Arsenic-Tech/LAV1/IMGS/vsp5 cl graph.png

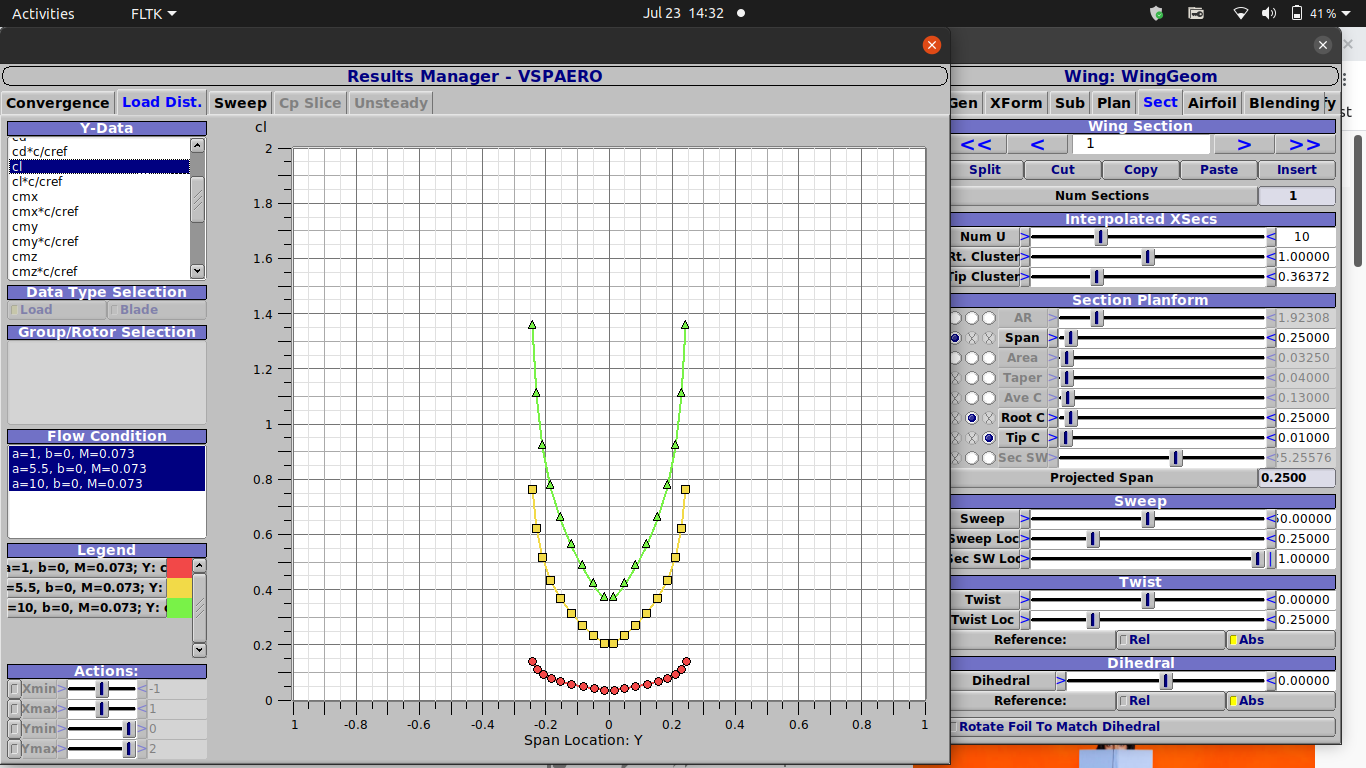
IMGS/vsp5 cl graph.png
