Arsenic-Tech/LAV1/IMGS/vsp7.1.convergence.CDtot.png

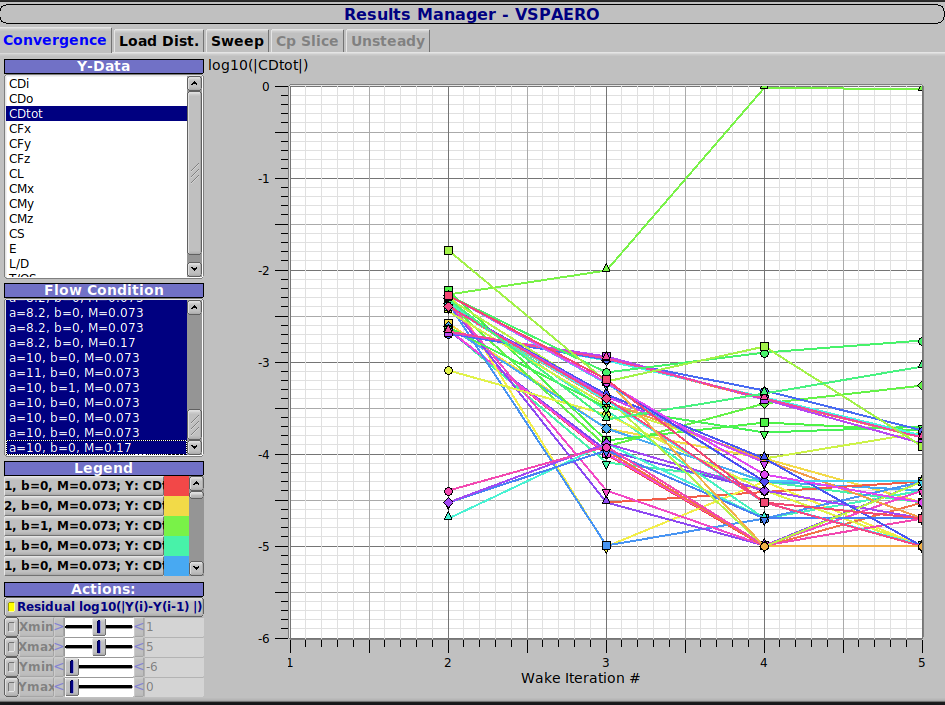
IMGS/vsp7.1.convergence.CDtot.png
