Arsenic-Tech/LAV1/IMGS/vsp7.1.convergence.L-D.png

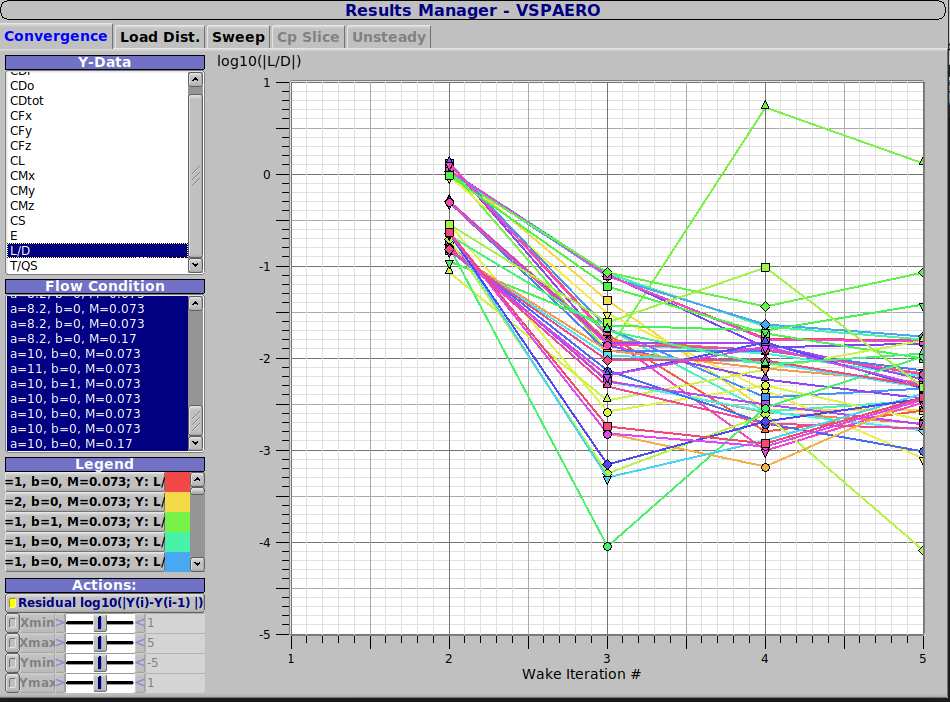
IMGS/vsp7.1.convergence.L-D.png
