Arsenic-Tech/LAV1/IMGS/vsp712.png

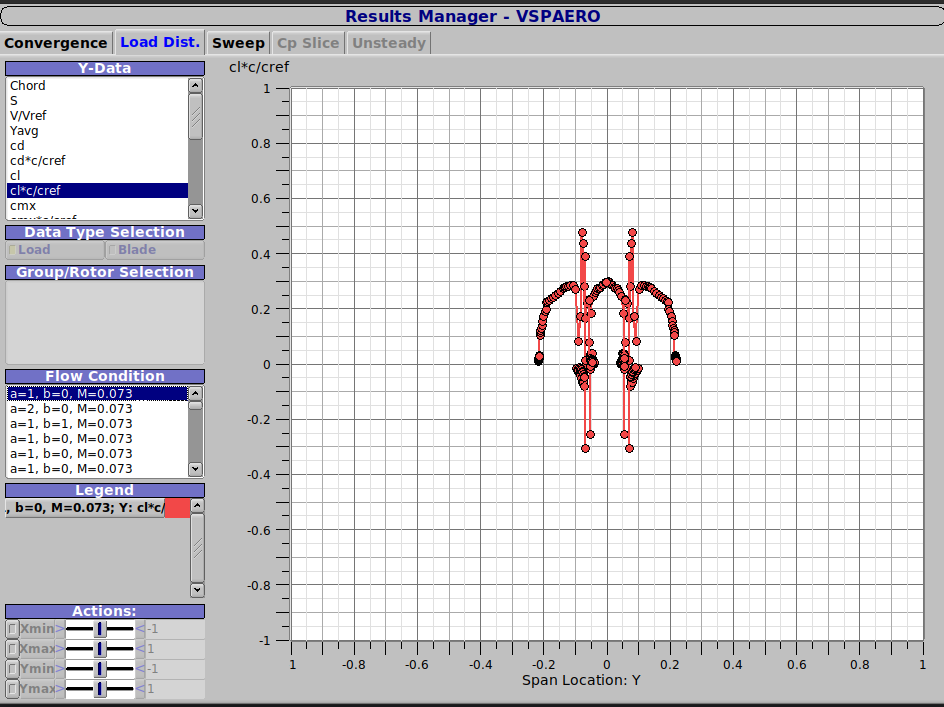
IMGS/vsp712.png
