Arsenic-Tech/LAV1/IMGS/vsp713.png

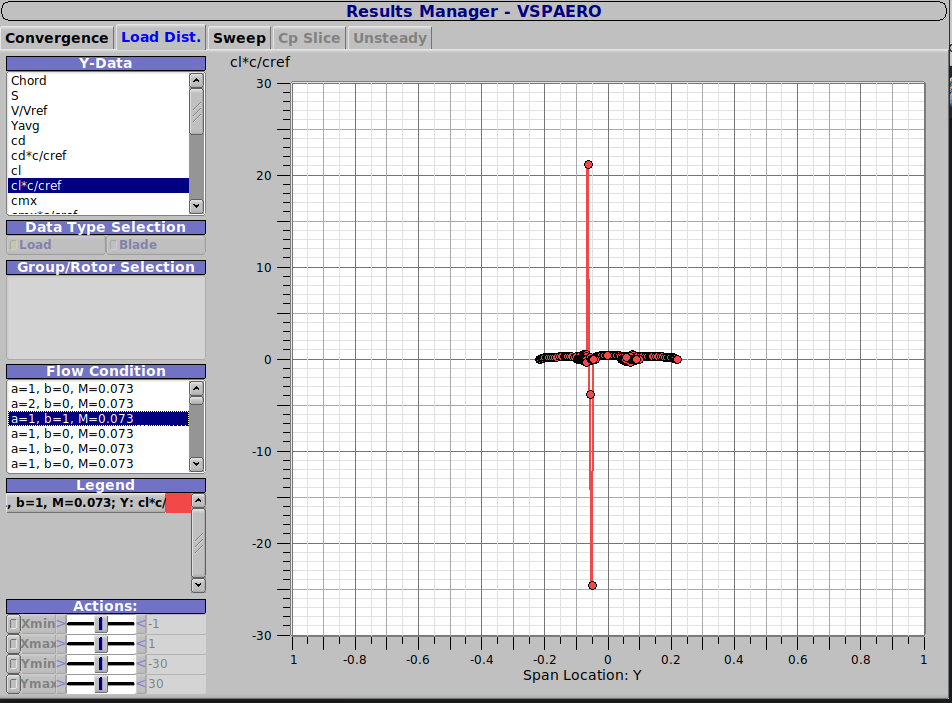
IMGS/vsp713.png
