Arsenic-Tech/LAV1/IMGS/vsp717.png

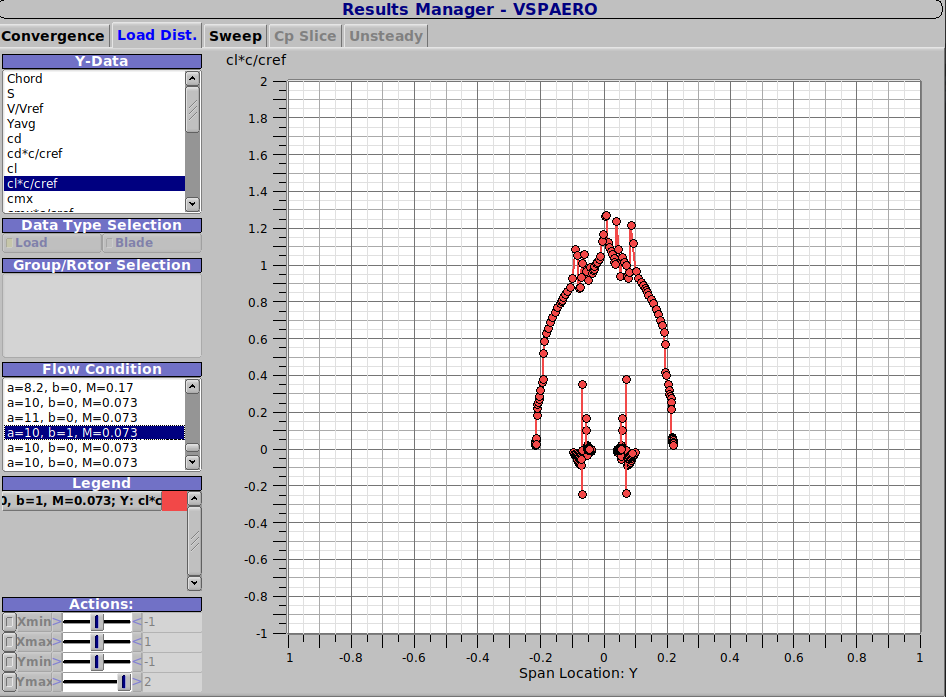
IMGS/vsp717.png
