Arsenic-Tech/LAV1/IMGS/vsp718.png

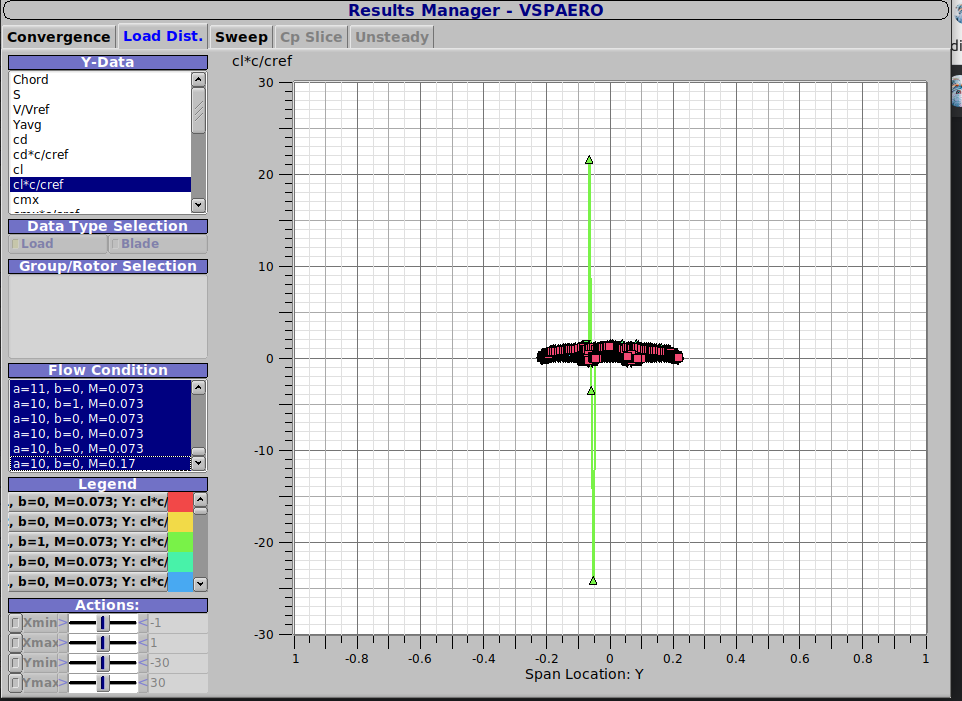
IMGS/vsp718.png
