Arsenic-Tech/LAV1/IMGS/vsp719.png

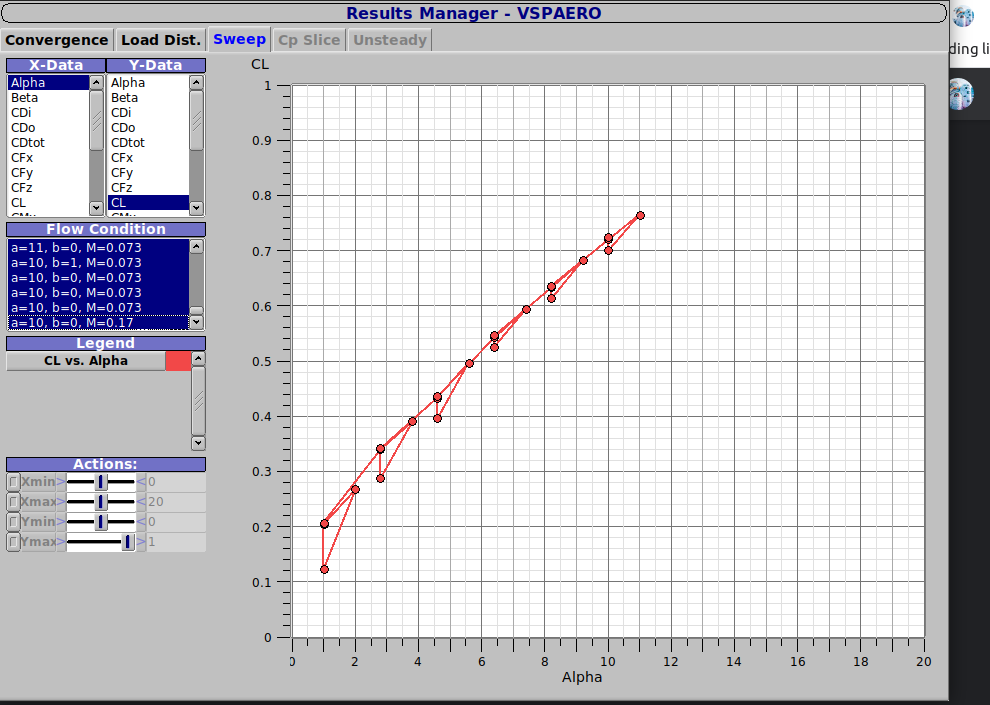
IMGS/vsp719.png
