Arsenic-Tech/LAV1/IMGS/VSP721.png

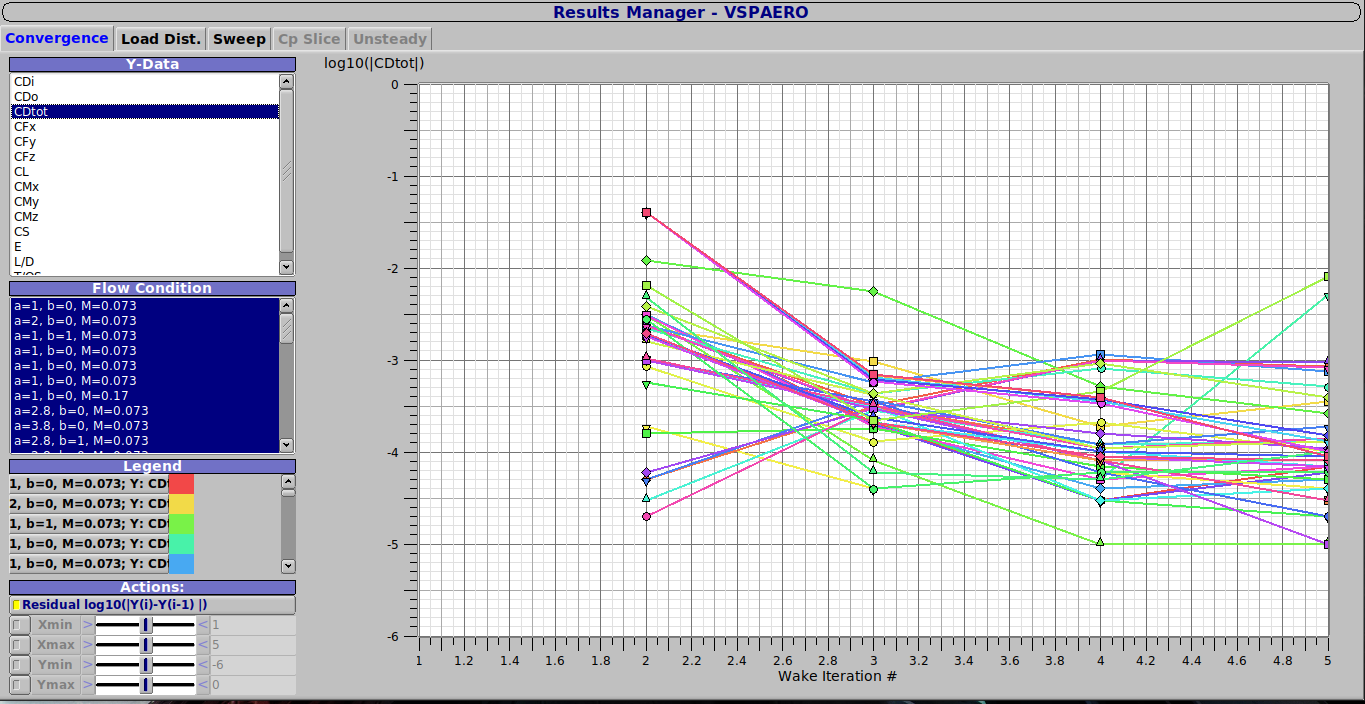
IMGS/VSP721.png
