Arsenic-Tech/LAV1/IMGS/vsp722.png

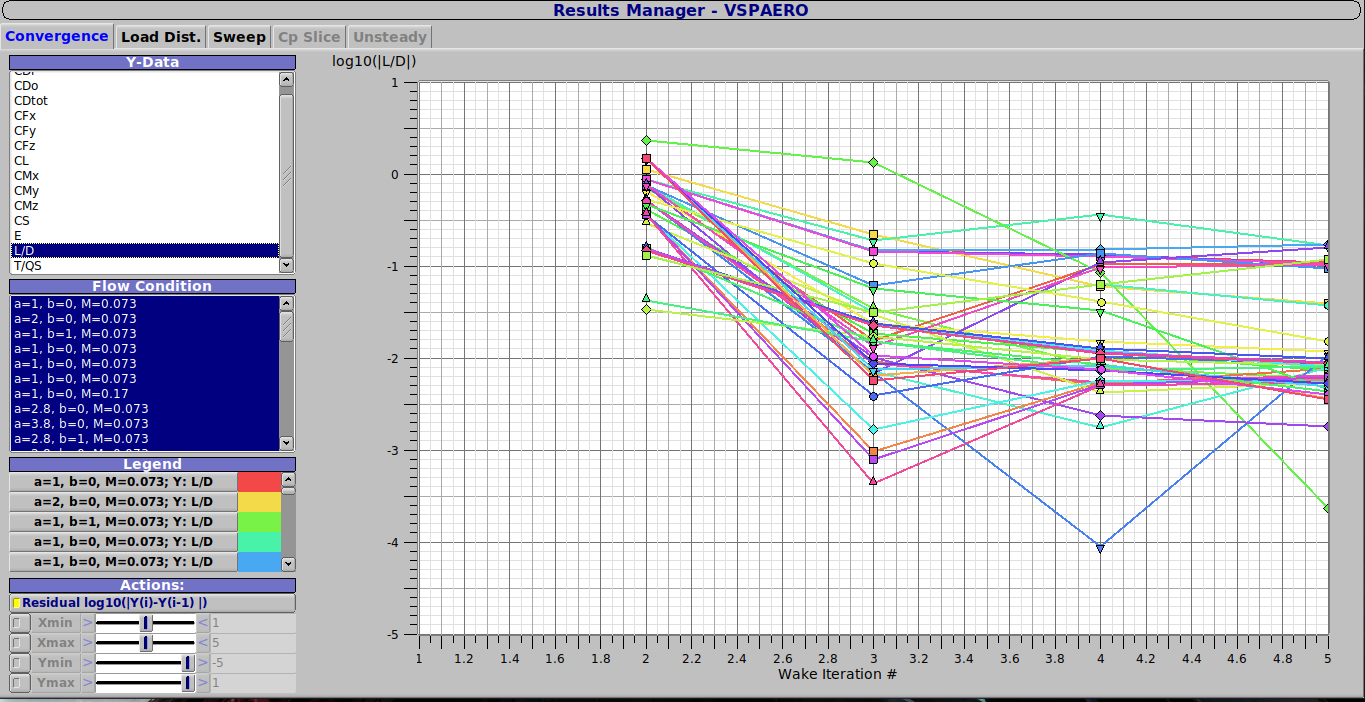
IMGS/vsp722.png
