Arsenic-Tech/LAV1/IMGS/vsp723.png

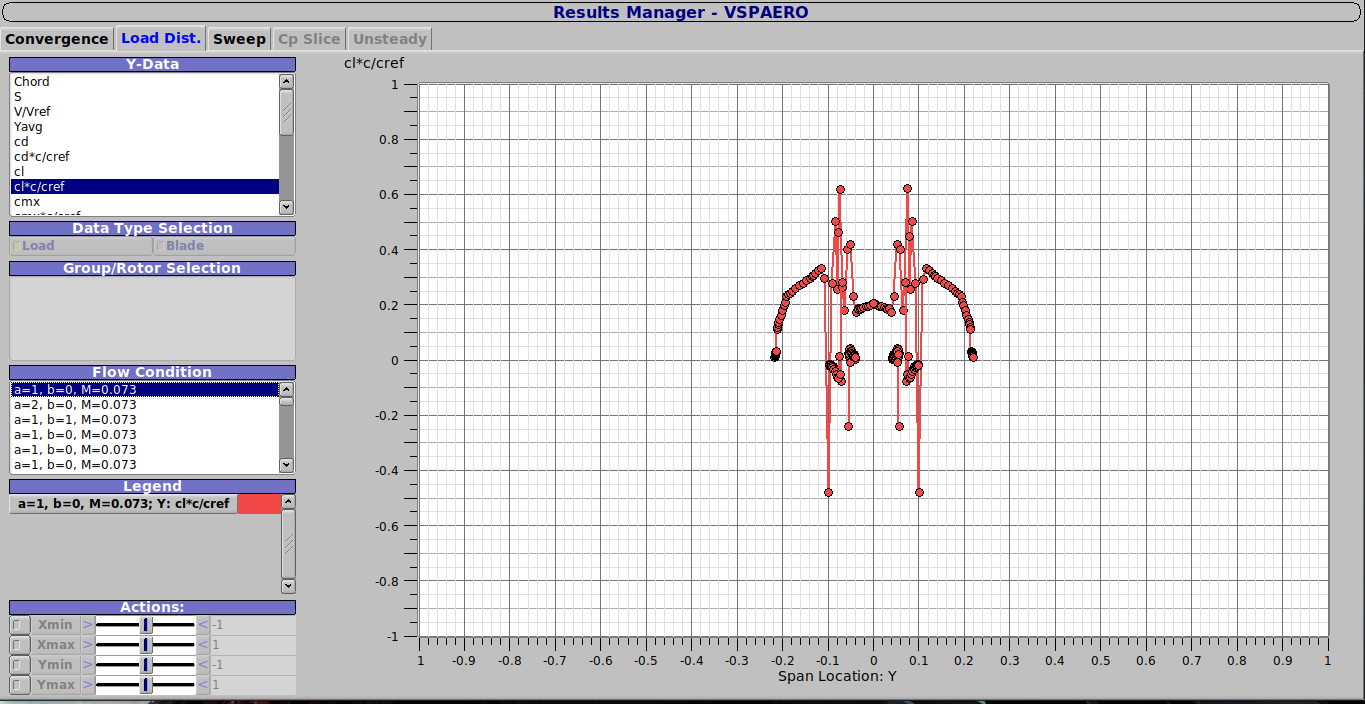
IMGS/vsp723.png
