Arsenic-Tech/LAV1/IMGS/vsp724.png

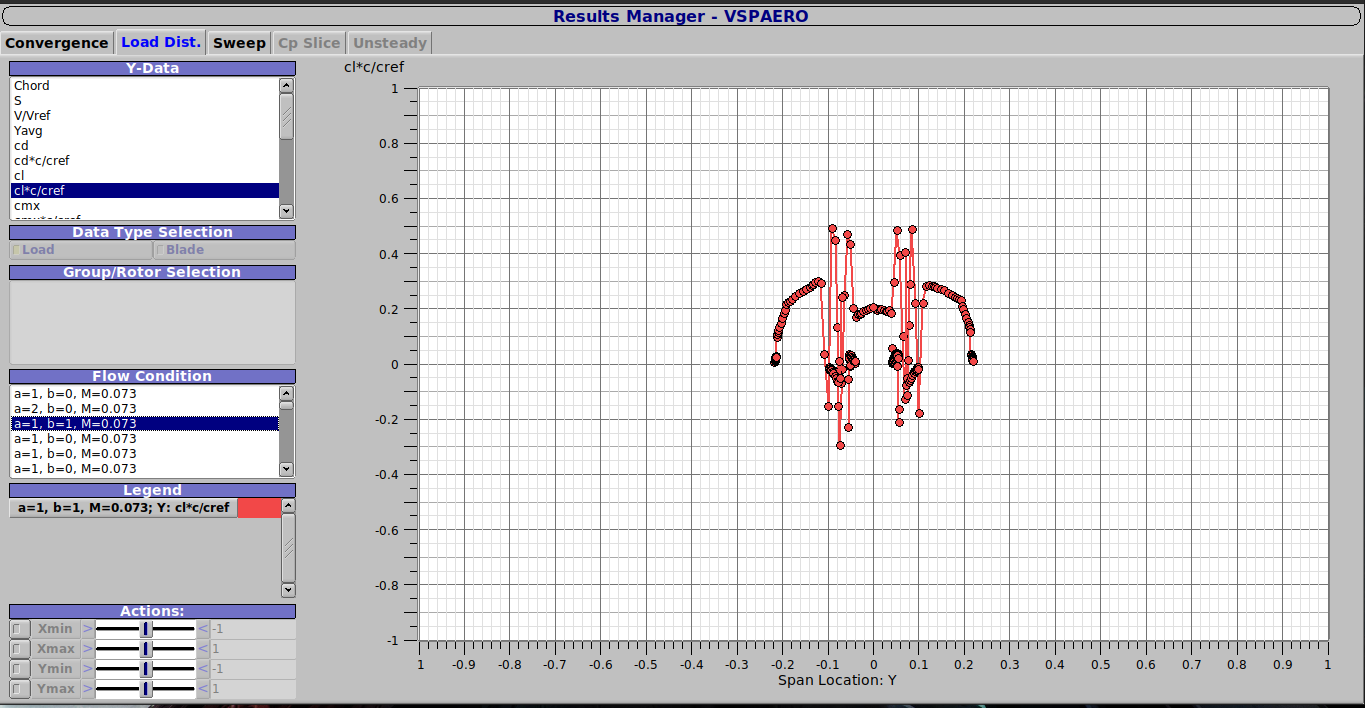
IMGS/vsp724.png
