Arsenic-Tech/LAV1/IMGS/vsp725.png

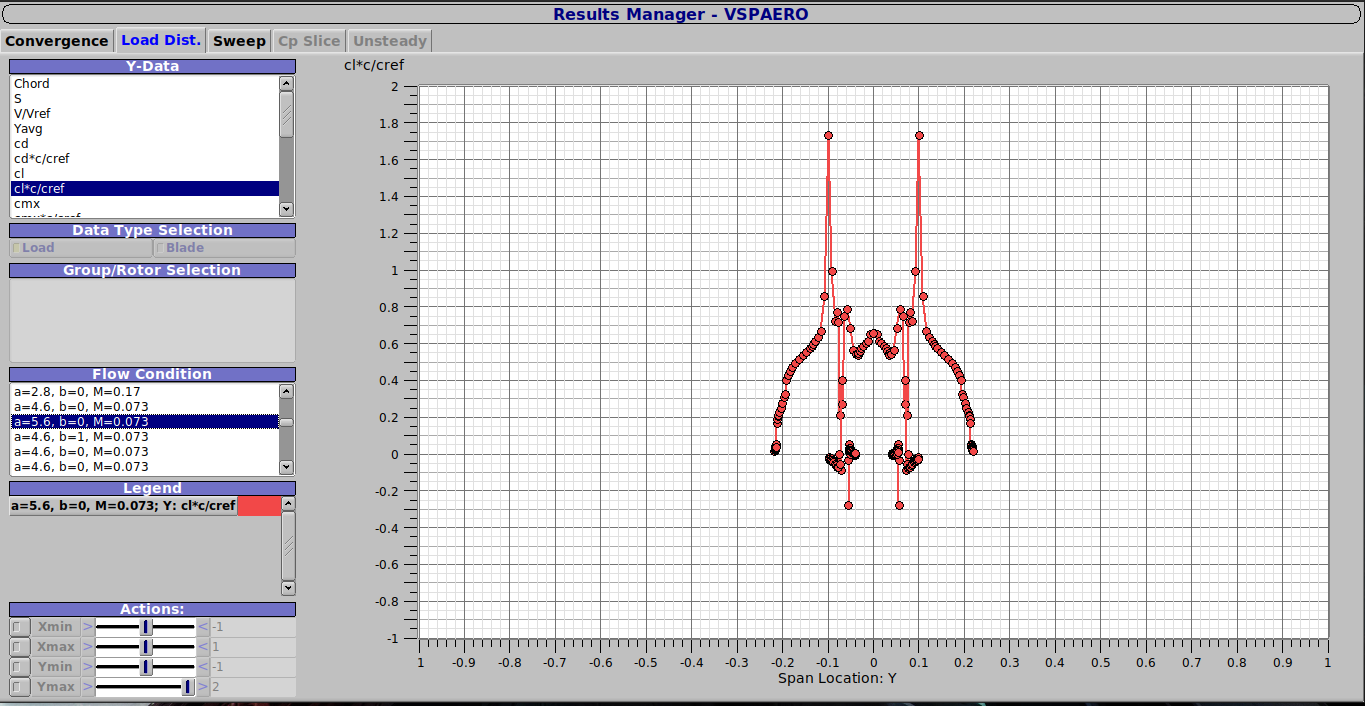
IMGS/vsp725.png
