Arsenic-Tech/LAV1/IMGS/vsp726.png

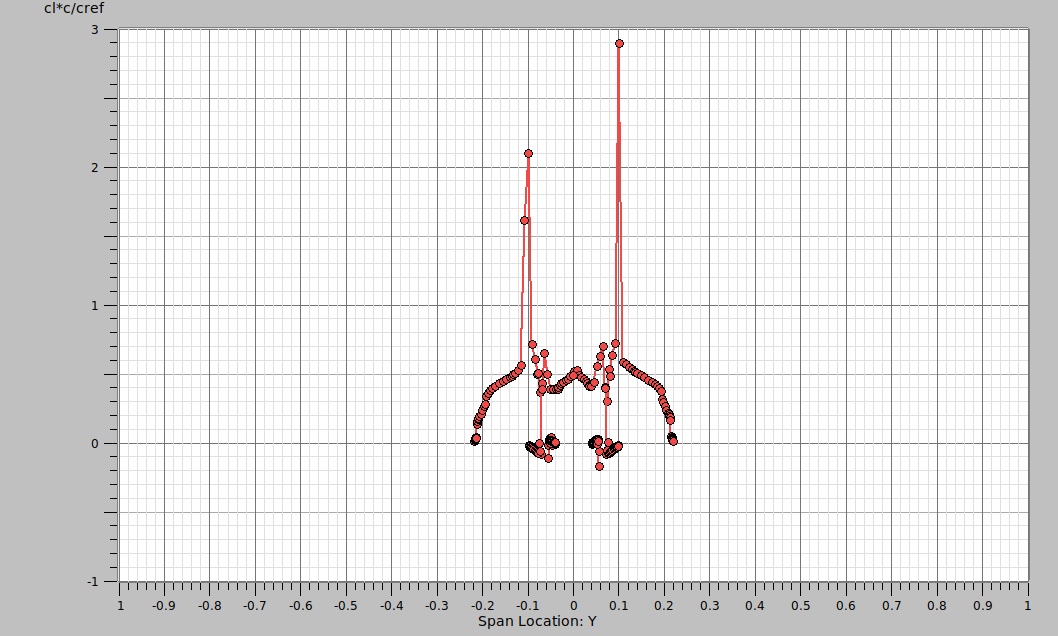
IMGS/vsp726.png
