Arsenic-Tech/LAV1/IMGS/vsp727.png

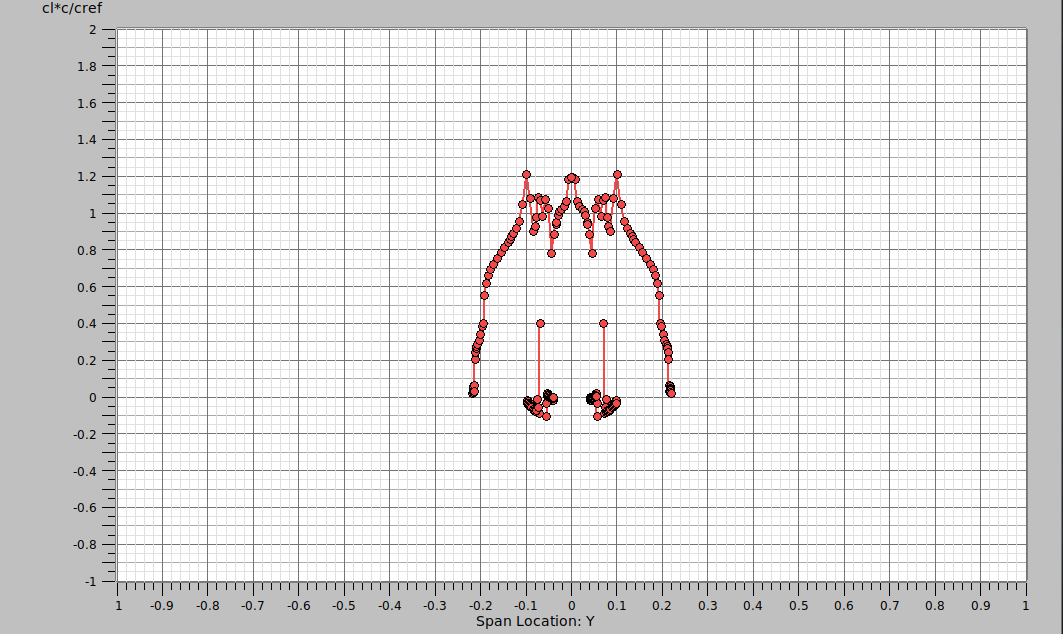
IMGS/vsp727.png
