Arsenic-Tech/LAV1/IMGS/vsp728.png

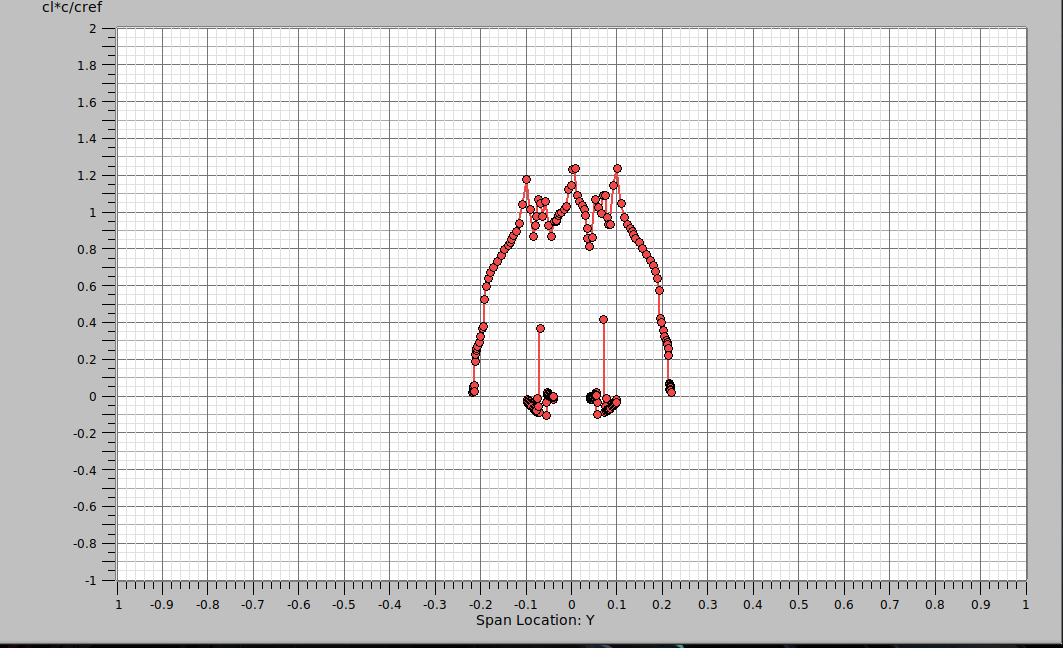
IMGS/vsp728.png
