Arsenic-Tech/LAV1/IMGS/vsp729.png

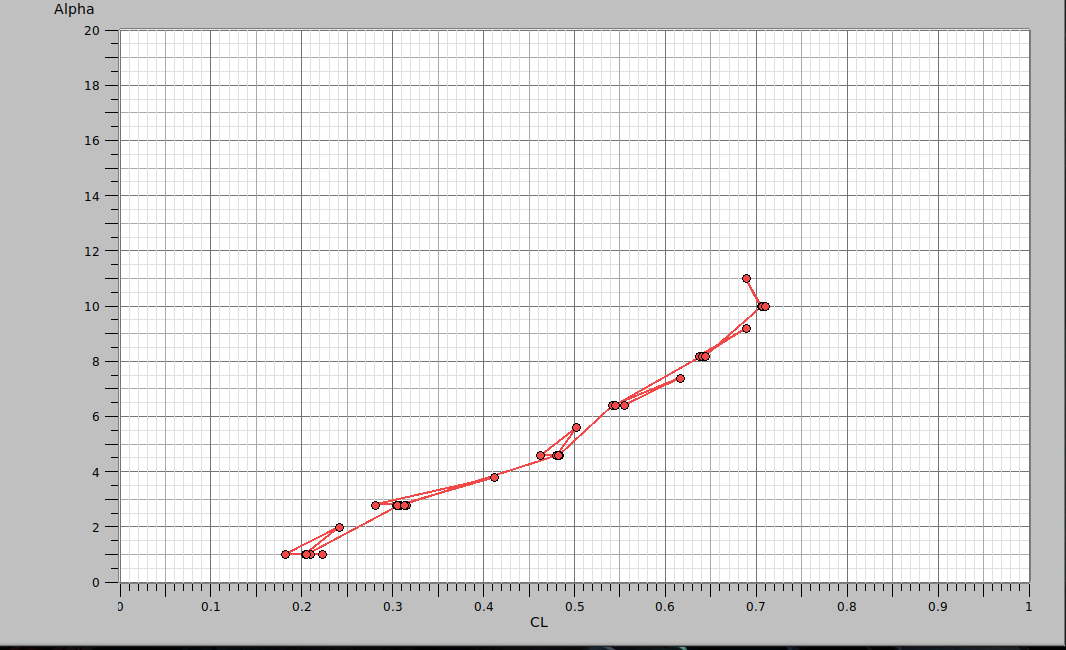
IMGS/vsp729.png
