Arsenic-Tech/LAV1/IMGS/vsp731.png

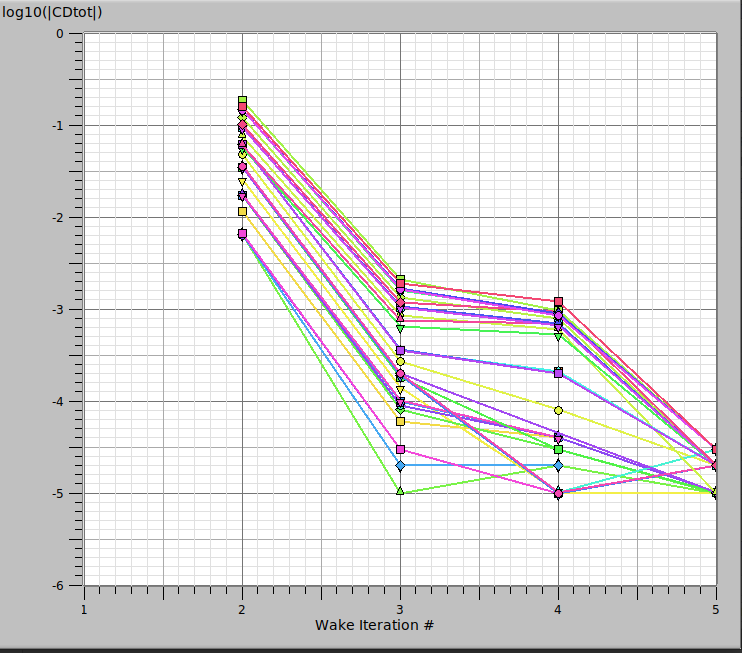
IMGS/vsp731.png
