Arsenic-Tech/LAV1/IMGS/vsp732.png

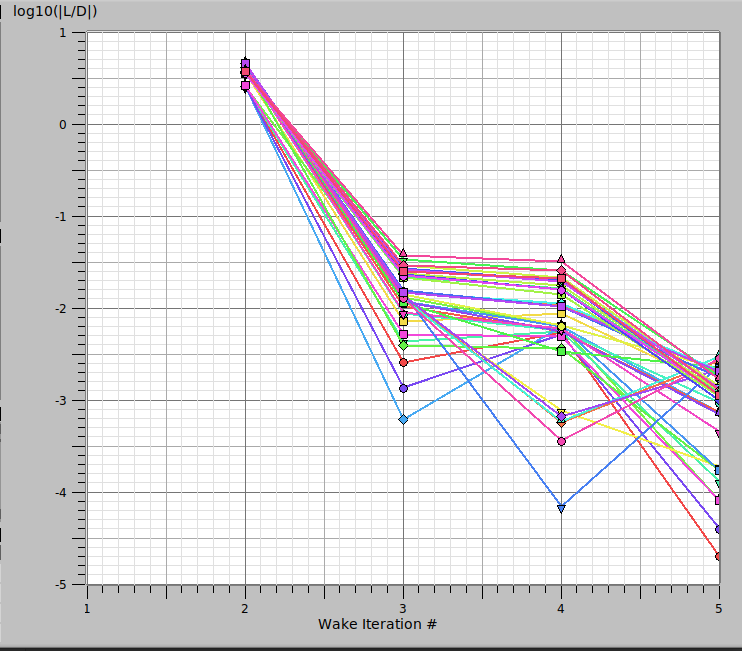
IMGS/vsp732.png
