Arsenic-Tech/LAV1/IMGS/vsp733.png

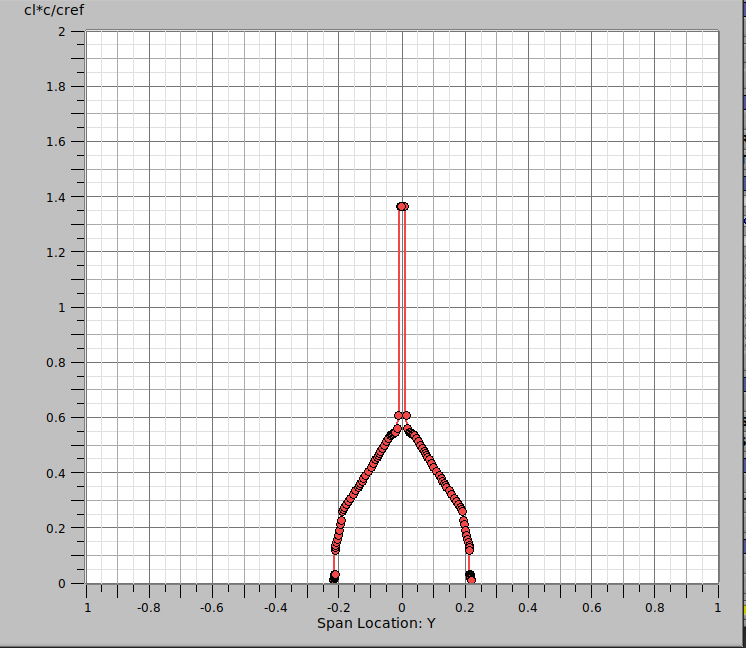
IMGS/vsp733.png
