Arsenic-Tech/LAV1/IMGS/vsp734.png

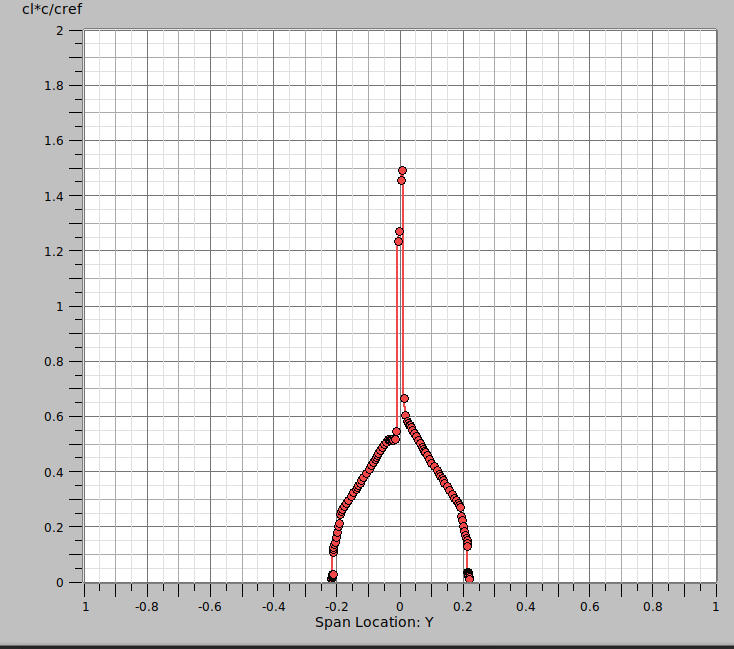
IMGS/vsp734.png
