Arsenic-Tech/LAV1/IMGS/vsp735.png

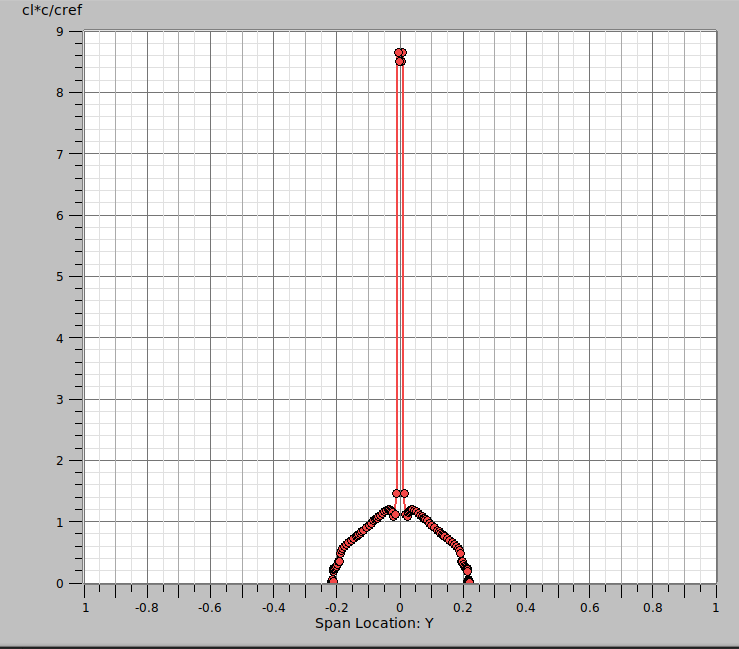
IMGS/vsp735.png
