Arsenic-Tech/LAV1/IMGS/vsp737.png

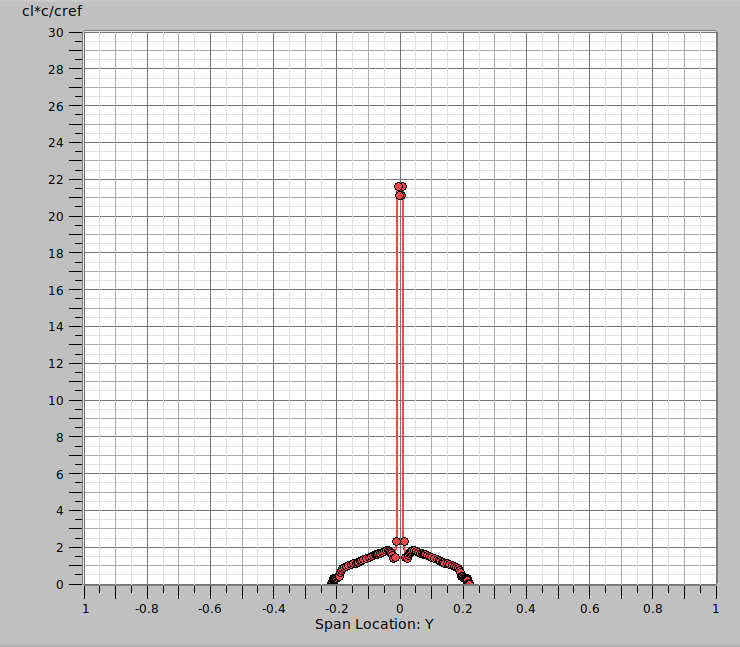
IMGS/vsp737.png
