Arsenic-Tech/LAV1/IMGS/vsp739.png

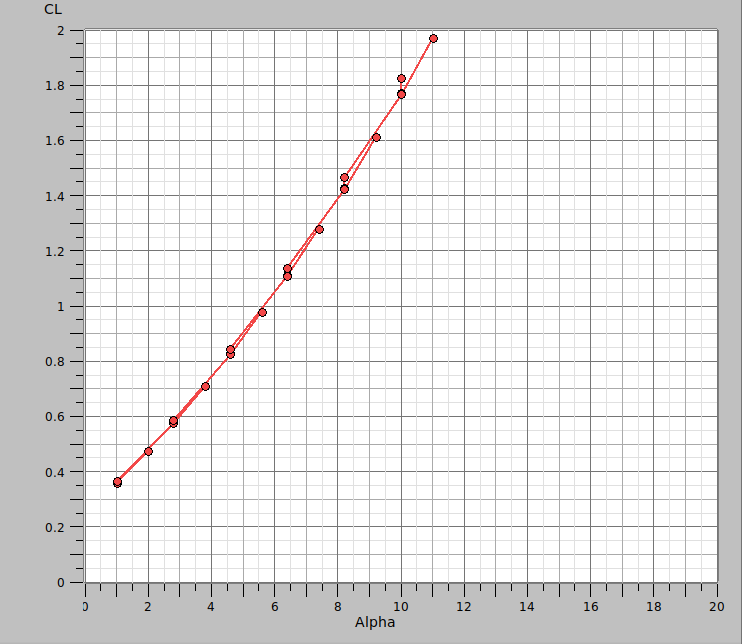
IMGS/vsp739.png
