Arsenic-Tech/LAV1/IMGS/vsp7110.png

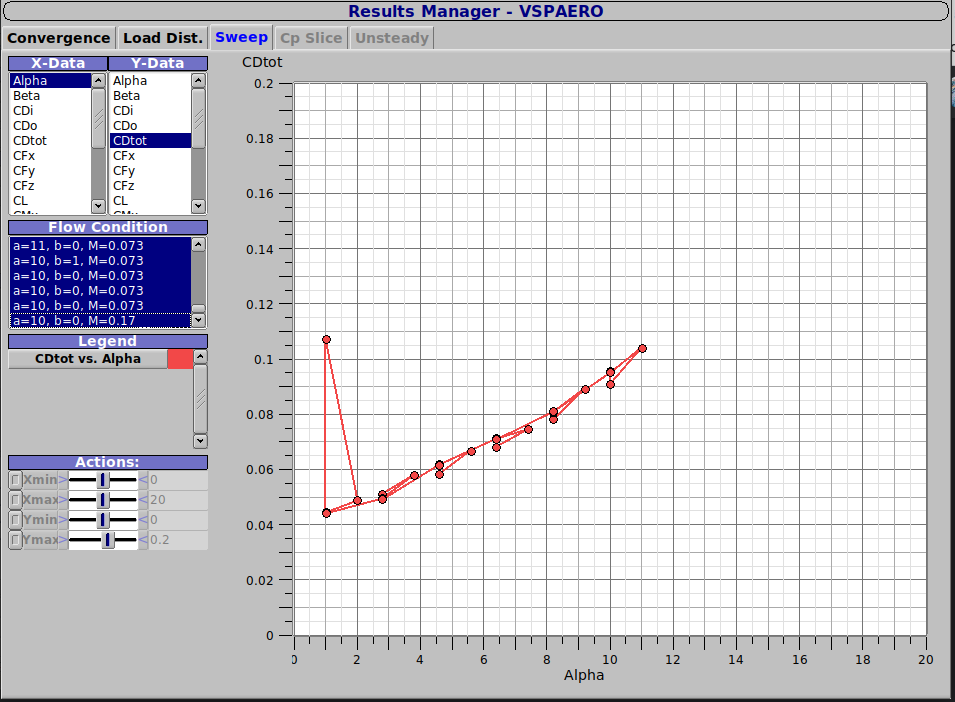
IMGS/vsp7110.png
