Arsenic-Tech/LAV1/IMGS/vsp7111.png

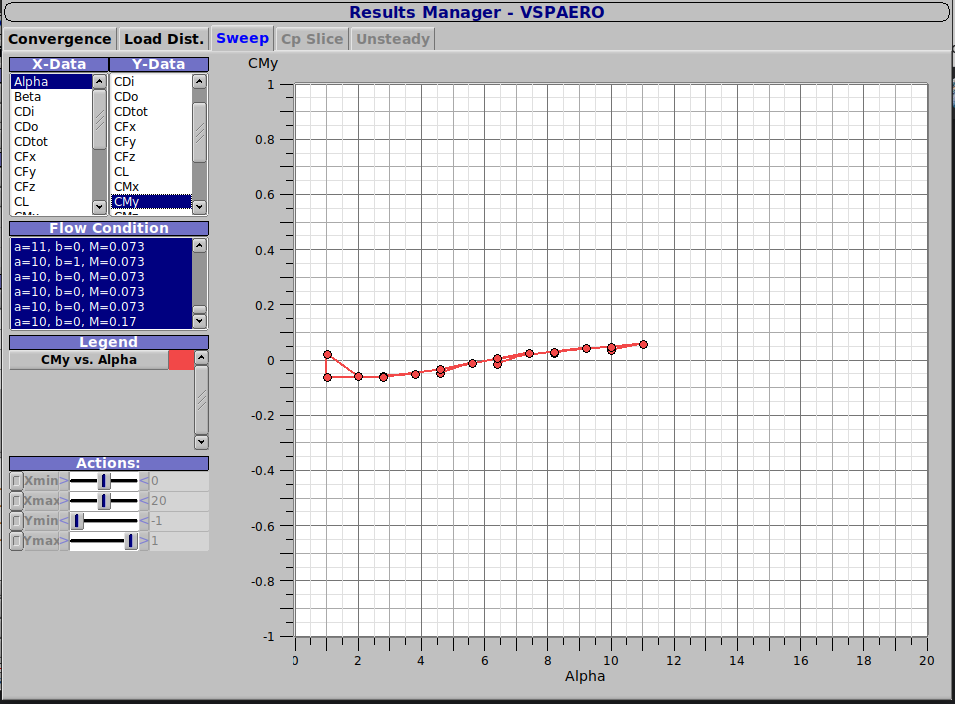
IMGS/vsp7111.png
