Arsenic-Tech/LAV1/IMGS/vsp7112.png

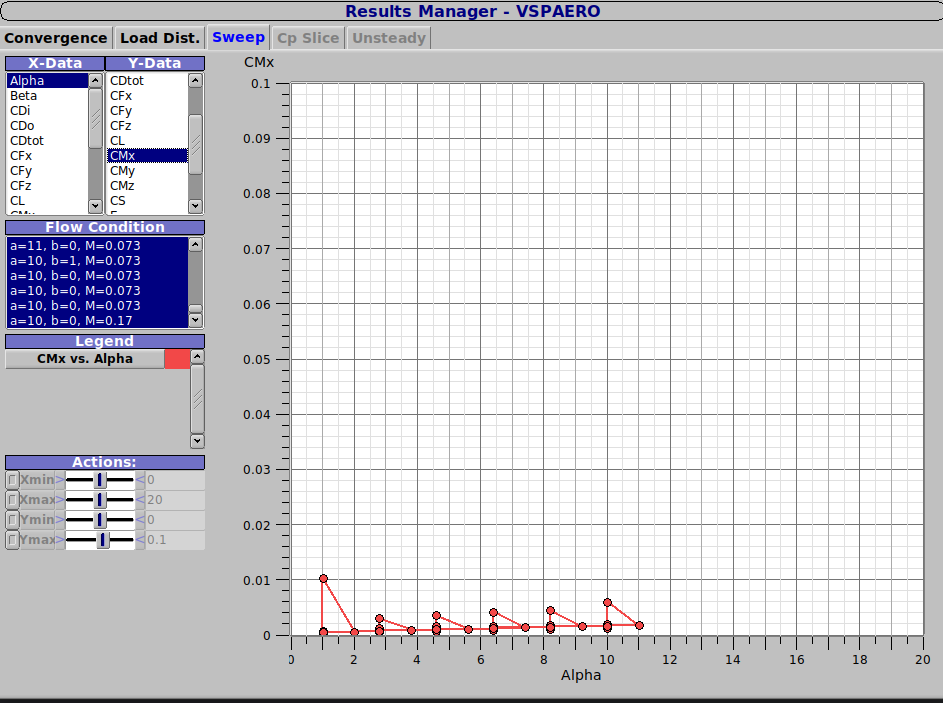
IMGS/vsp7112.png
