Arsenic-Tech/LAV1/IMGS/vsp7113.png

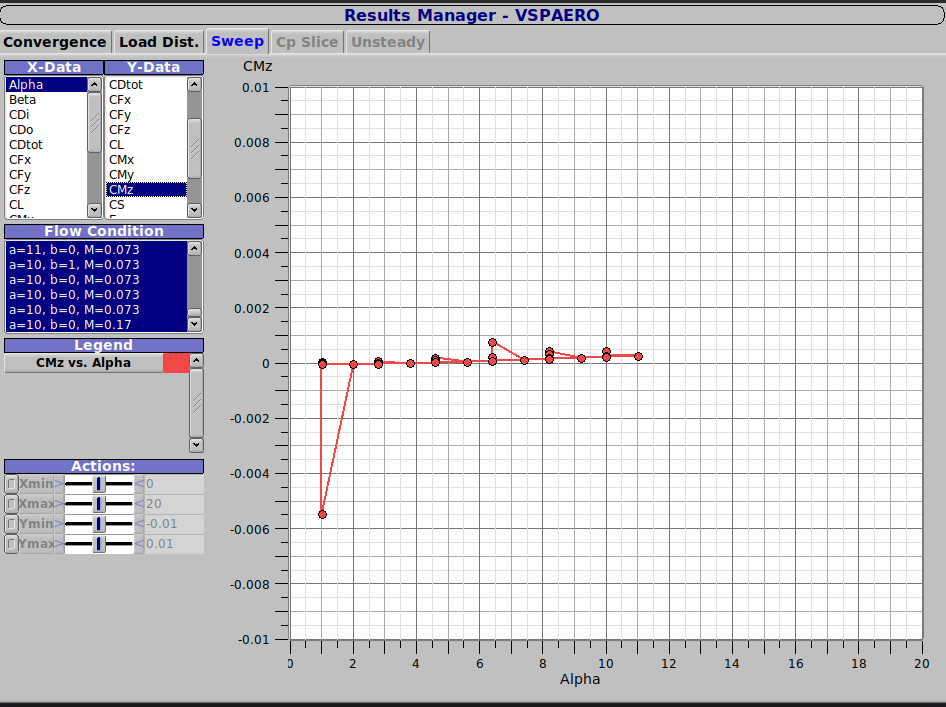
IMGS/vsp7113.png
