Arsenic-Tech/LAV1/IMGS/vsp7114.png

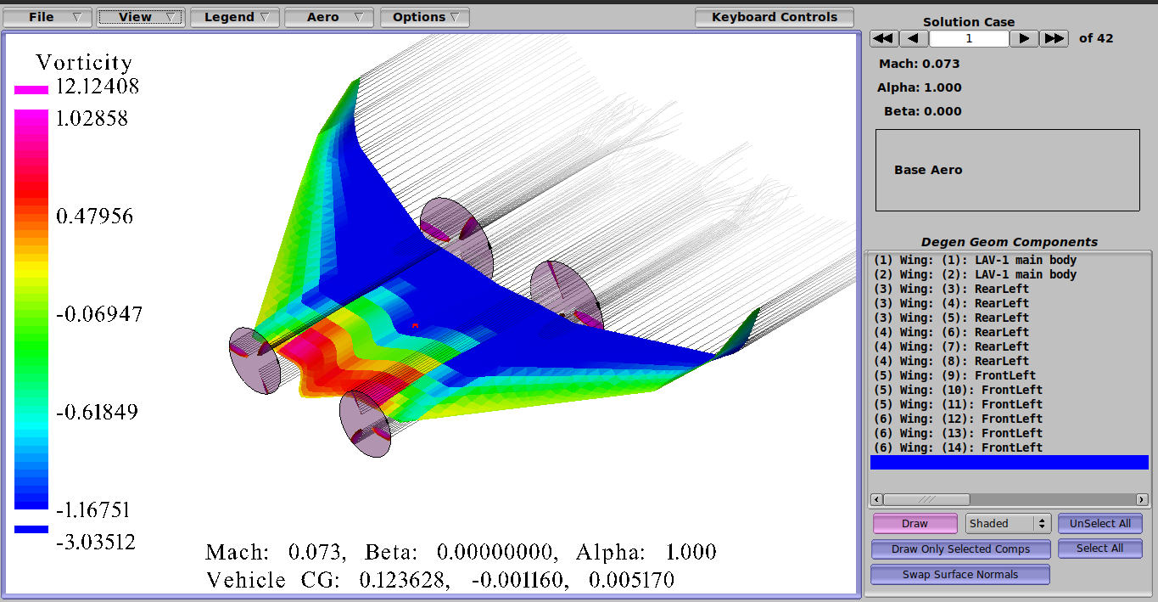
IMGS/vsp7114.png
