Arsenic-Tech/LAV1/IMGS/vsp7116.png

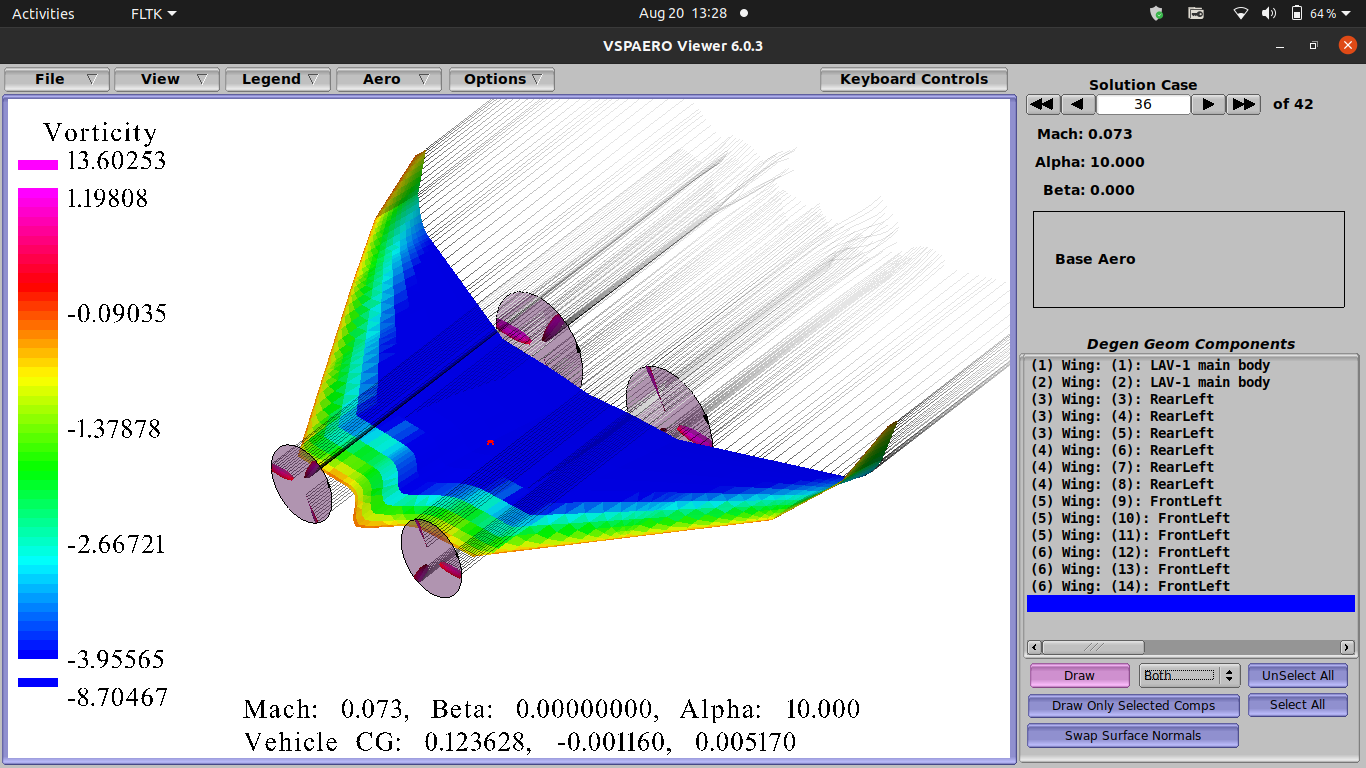
IMGS/vsp7116.png
