Arsenic-Tech/LAV1/IMGS/vsp7210.png

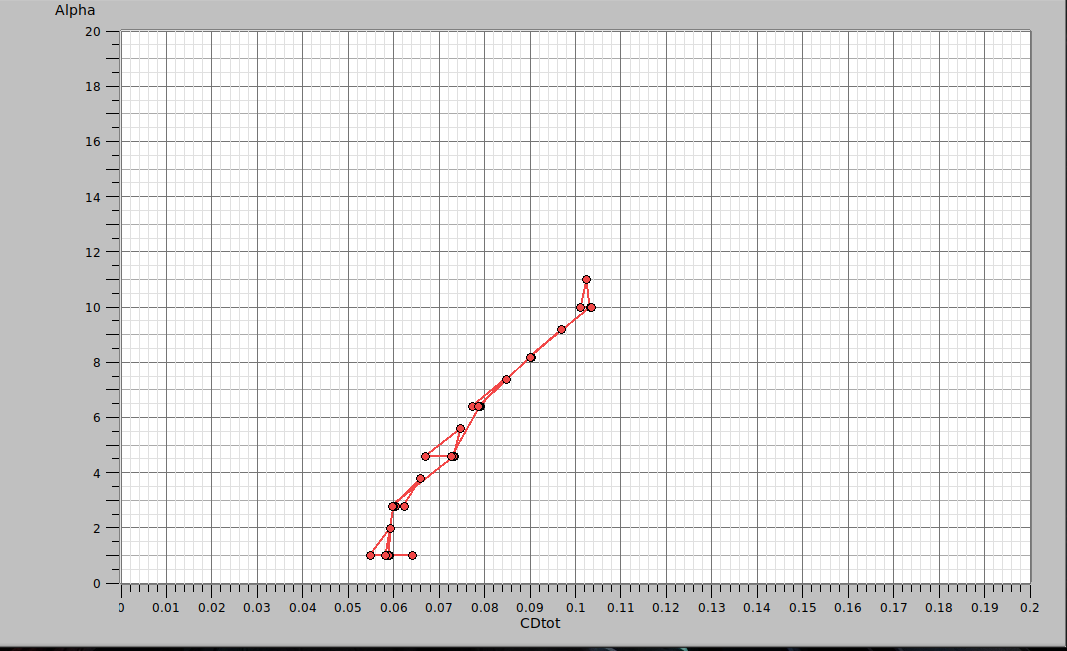
IMGS/vsp7210.png
