Arsenic-Tech/LAV1/IMGS/vsp7211.png

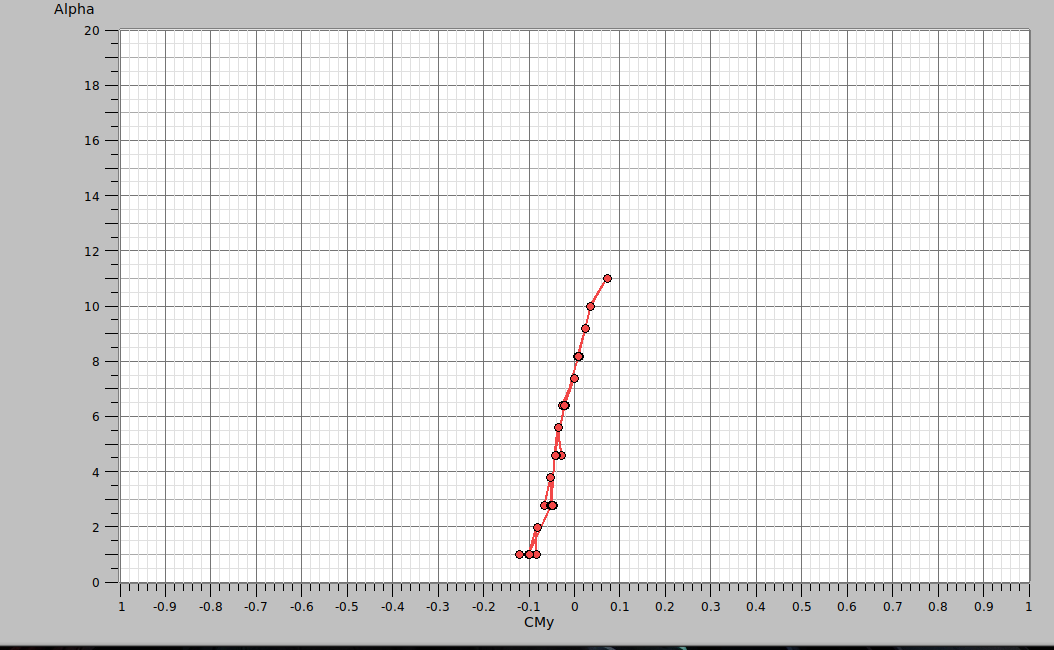
IMGS/vsp7211.png
