Arsenic-Tech/LAV1/IMGS/vsp7212.png

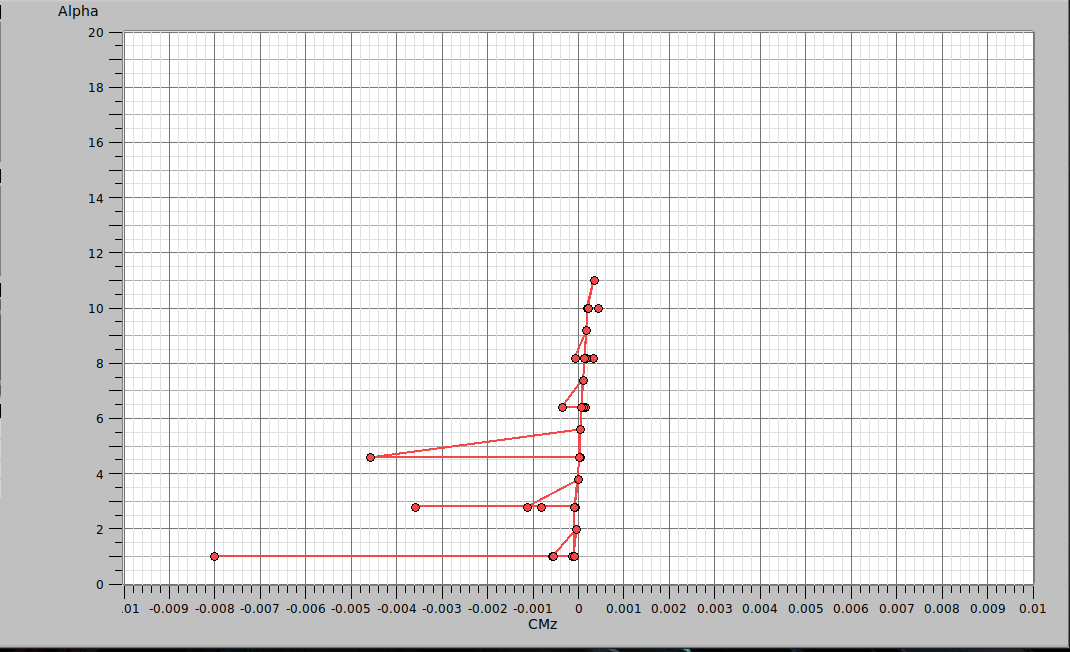
IMGS/vsp7212.png
