Arsenic-Tech/LAV1/IMGS/vsp7213.png

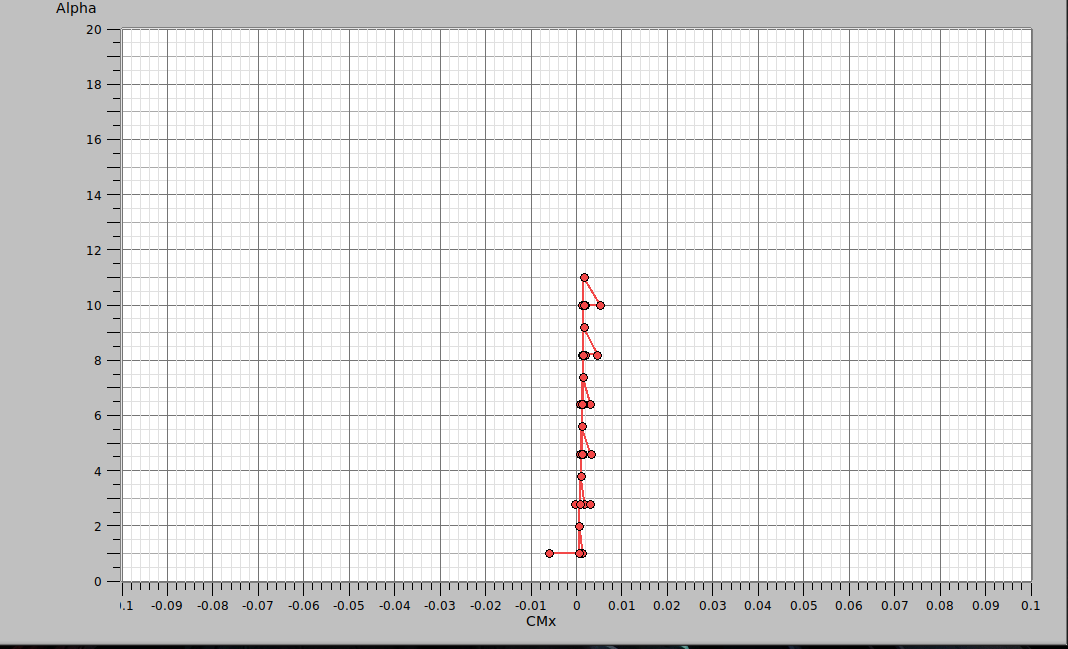
IMGS/vsp7213.png
