Arsenic-Tech/LAV1/IMGS/vsp7214.png

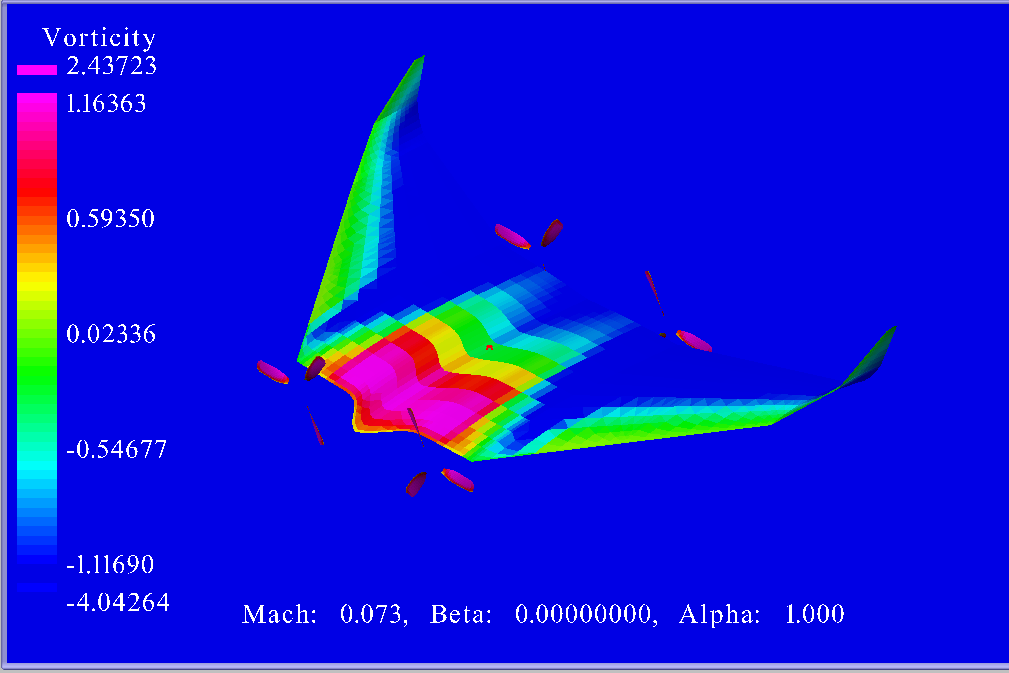
IMGS/vsp7214.png
