Arsenic-Tech/LAV1/IMGS/vsp7215.png

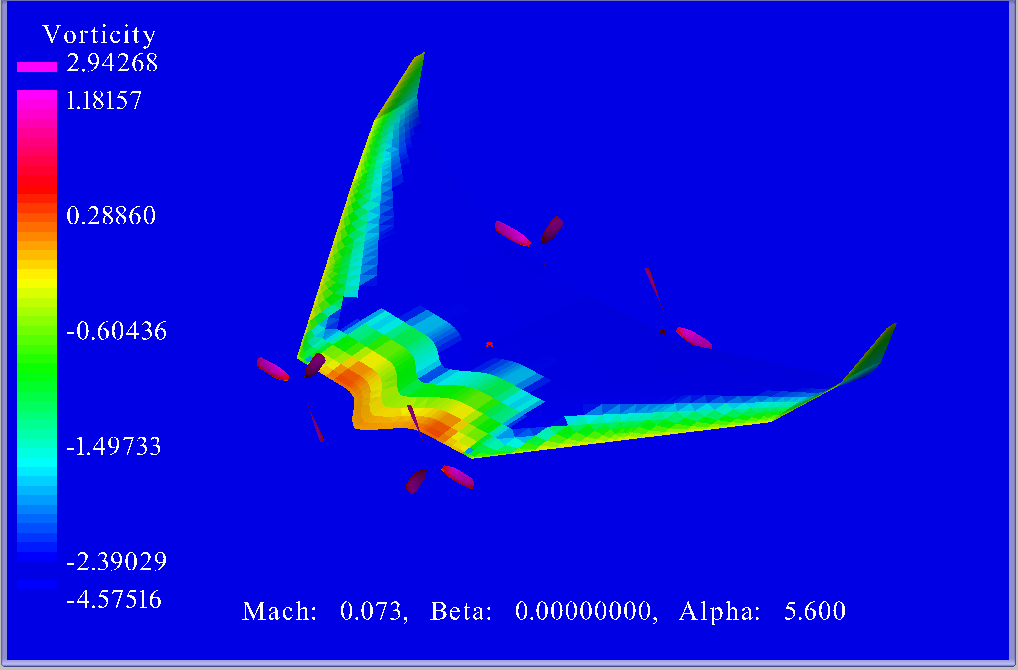
IMGS/vsp7215.png
