Arsenic-Tech/LAV1/IMGS/vsp7310.png

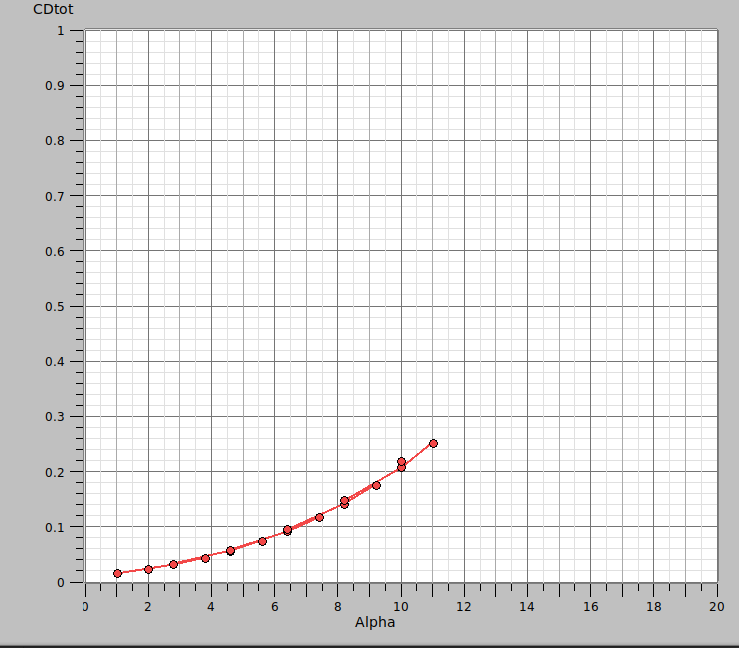
IMGS/vsp7310.png
