Arsenic-Tech/LAV1/IMGS/vsp7311.png

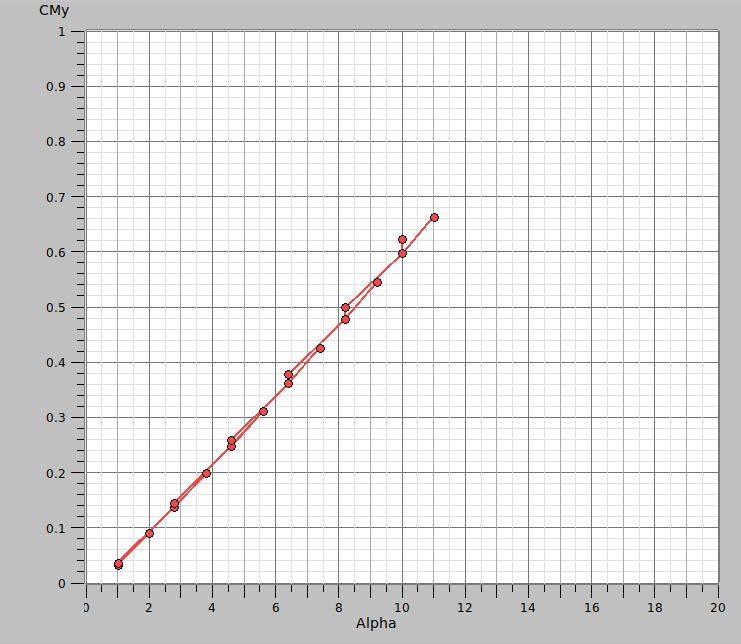
IMGS/vsp7311.png
