Arsenic-Tech/LAV1/IMGS/vsp7312.png

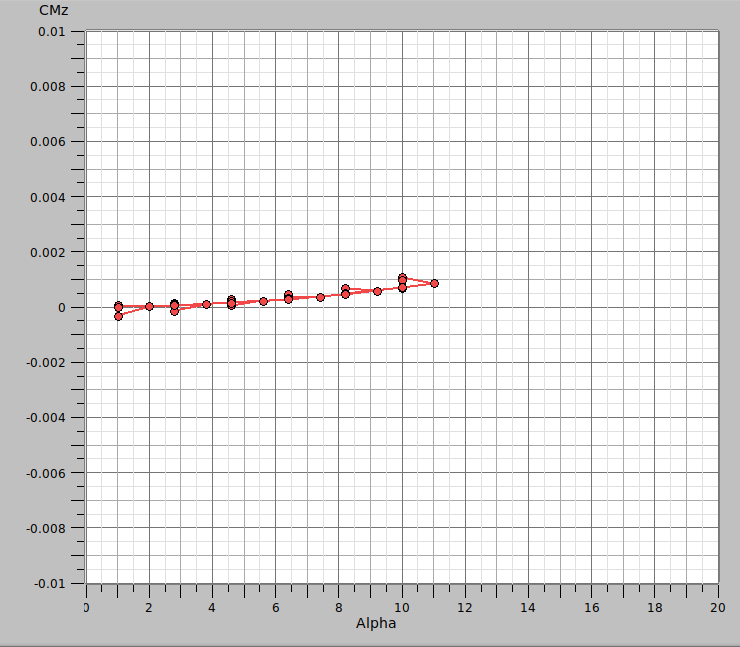
IMGS/vsp7312.png
