Arsenic-Tech/LAV1/IMGS/vsp7314.png

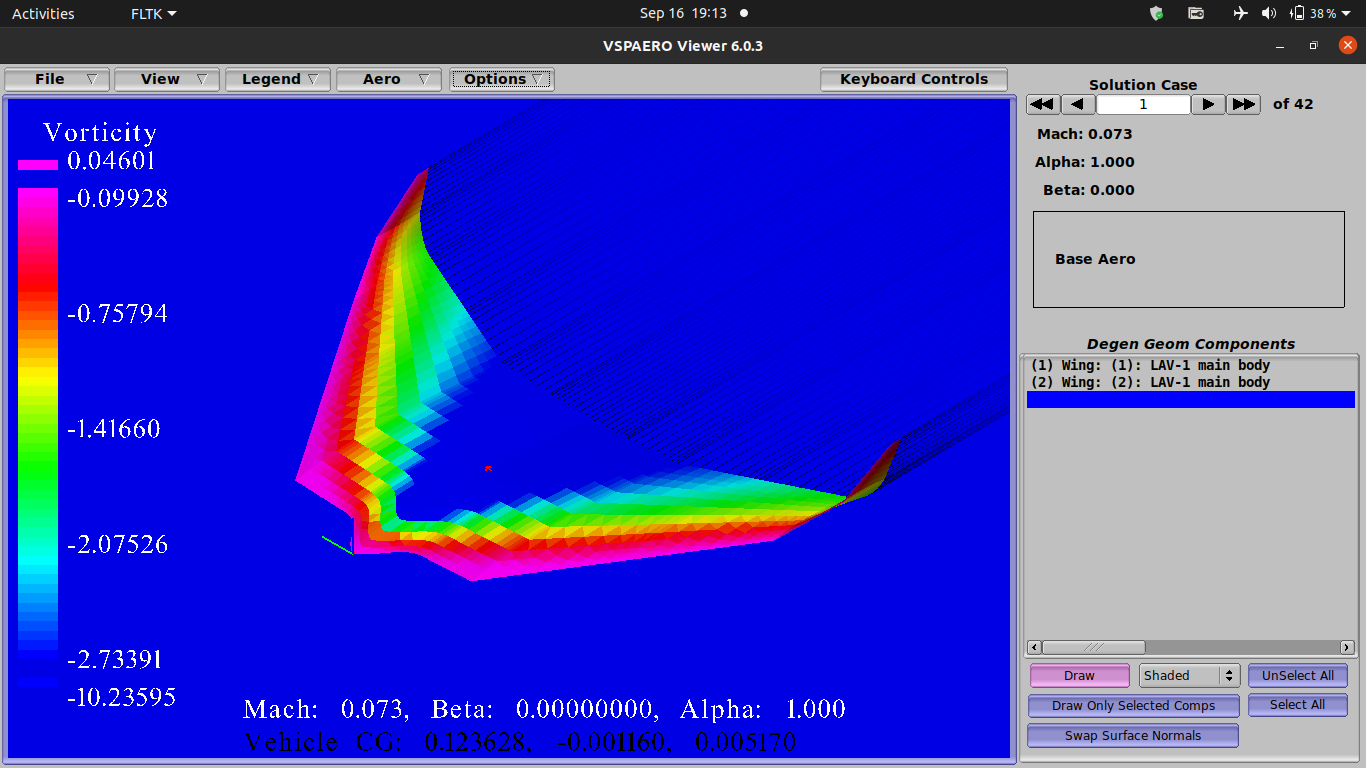
IMGS/vsp7314.png
